Envy-Gt/shining/images/3D_View_Shining/3D_view_1.png

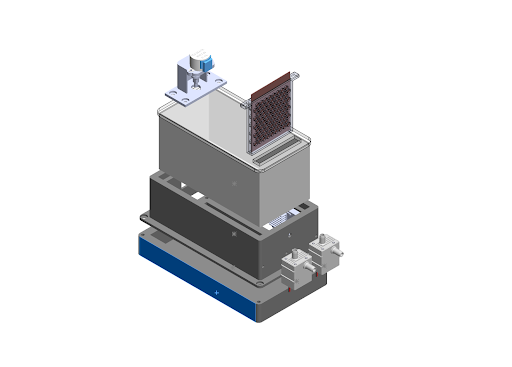
images/3D_View_Shining/3D_view_1.png
