Envy-Gt/shining/images/pictures/image_embout.jpeg

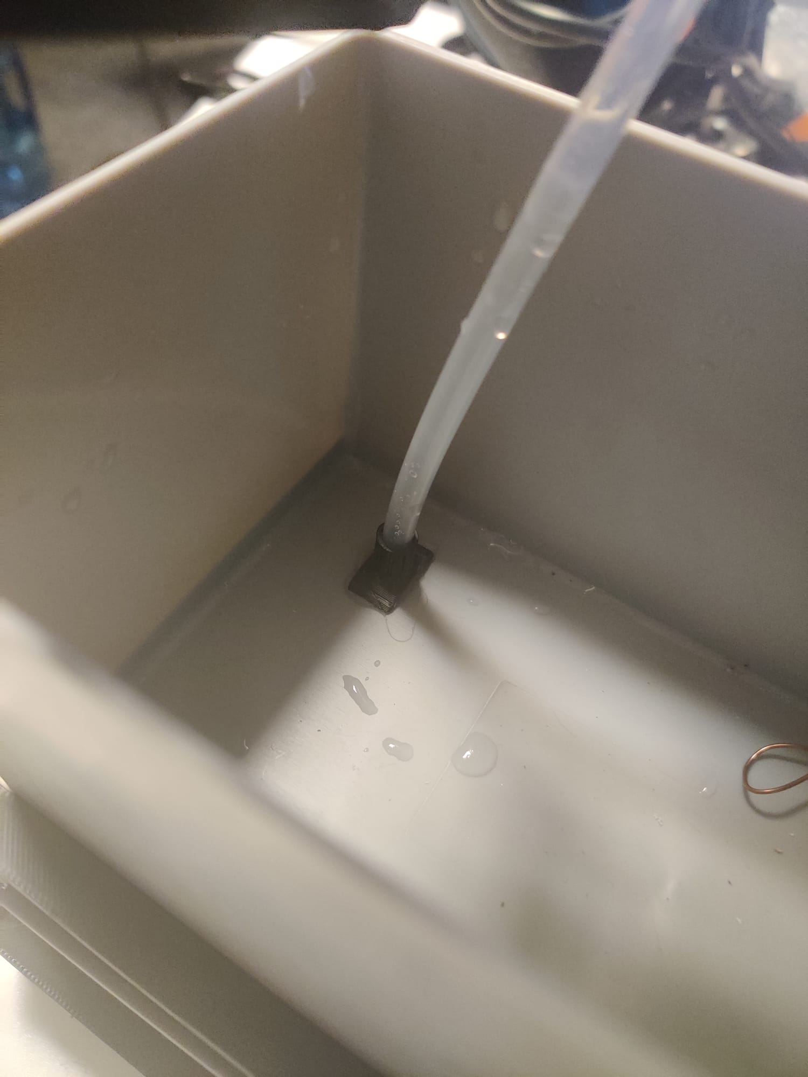
images/pictures/image_embout.jpeg
