Envy-Gt/shining/images/pictures/image_front.jpeg

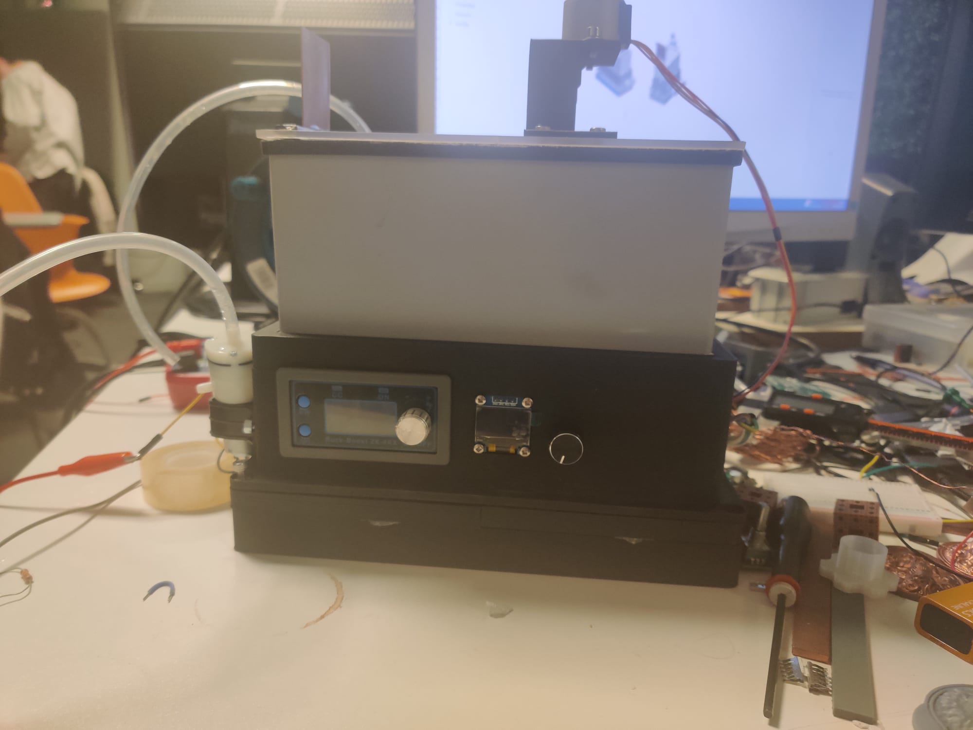
images/pictures/image_front.jpeg
