Envy-Gt/shining/images/pictures/image_inside_2.jpeg

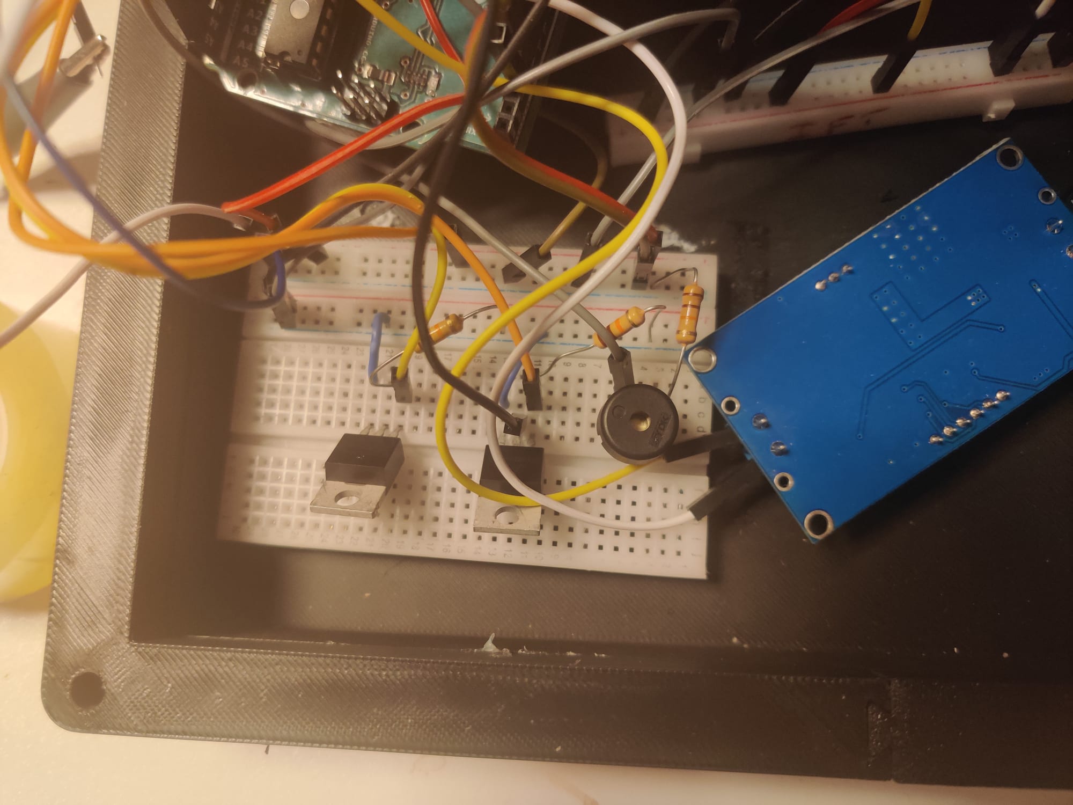
images/pictures/image_inside_2.jpeg
