Envy-Gt/shining/SLPRT files/Stepper motor 28BYJ-48 5V.SLDPRT

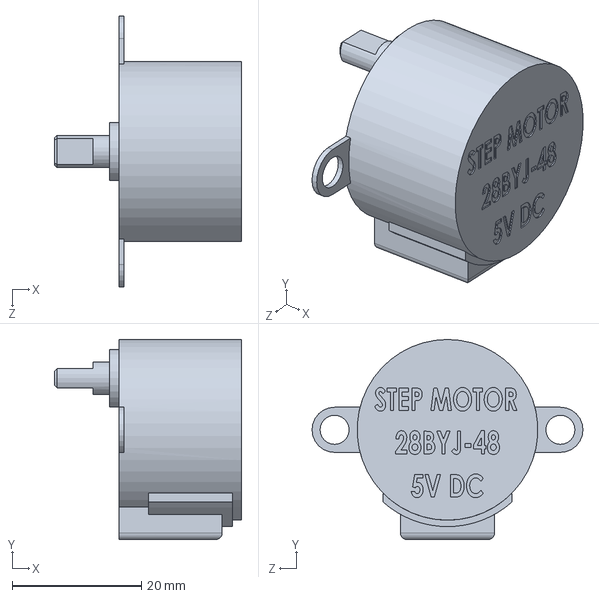
[picture p35: CAD file, 2026-01-27]
SLPRT files/Stepper motor 28BYJ-48 5V.SLDPRT
29.0 x 31.0 x 42.0 mm
