Envy-Gt/shining/SLPRT files/User Library-QR30E.SLDPRT

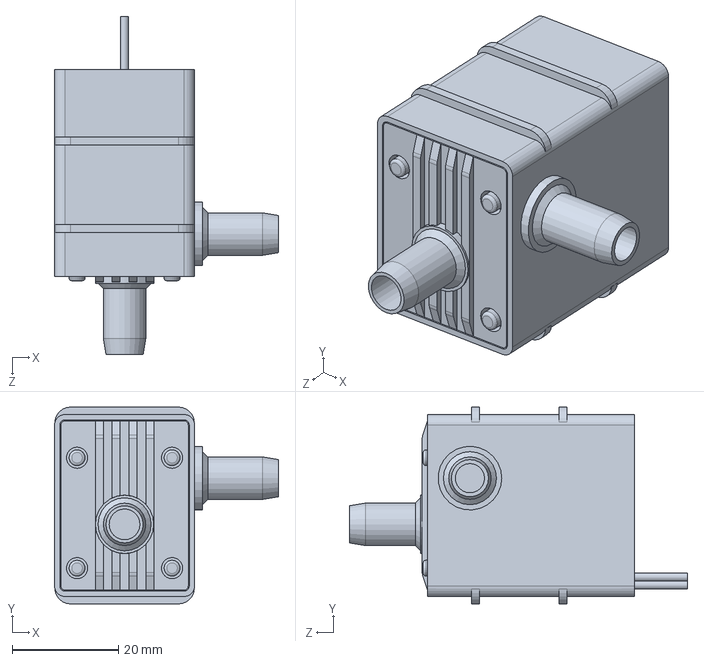
[picture p36: CAD file, 2026-01-27]
SLPRT files/User Library-QR30E.SLDPRT
42.2 x 37.1 x 63.7 mm
