Envy-Gt/shining/images/wiring/wiring_encoder.png

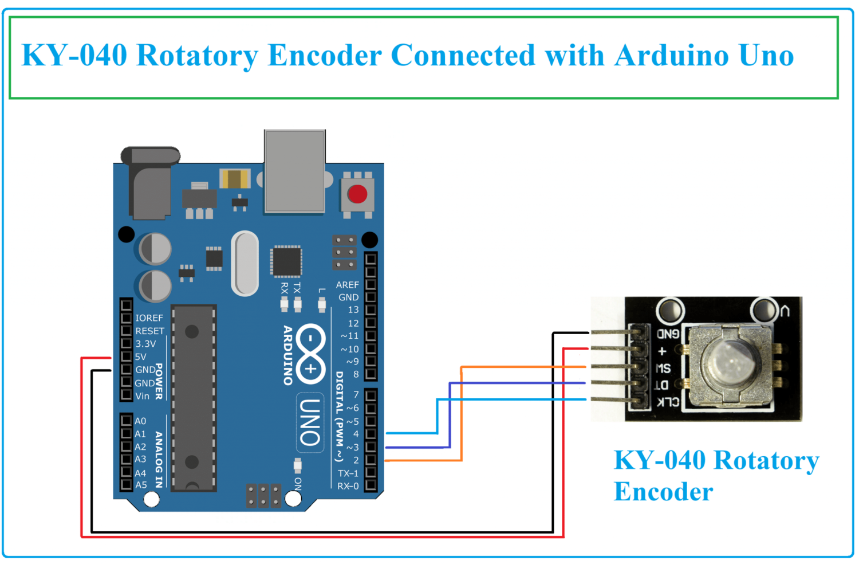
images/wiring/wiring_encoder.png
