Envy-Gt/shining/images/wiring/wiring_screen.jpg

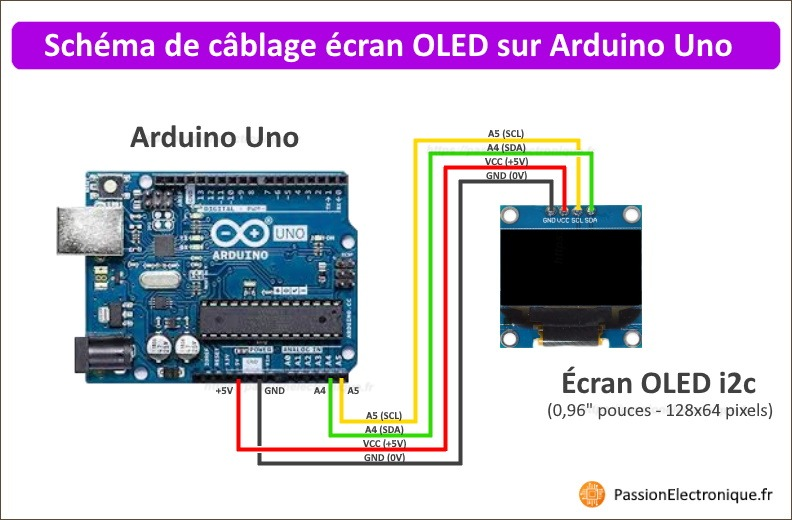
images/wiring/wiring_screen.jpg
